ckuzma/dipole-antenna/media/02-element-holder-beta-tinkercad.png

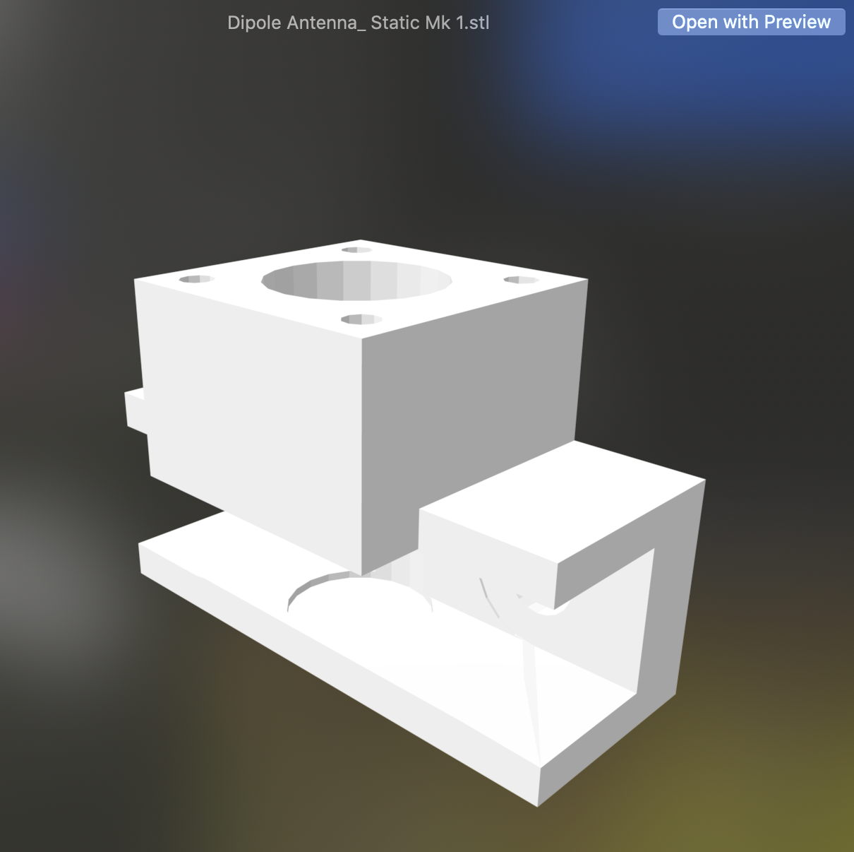
media/02-element-holder-beta-tinkercad.png
