ckuzma/dipole-antenna/media/03-so239-plug-freecad.png

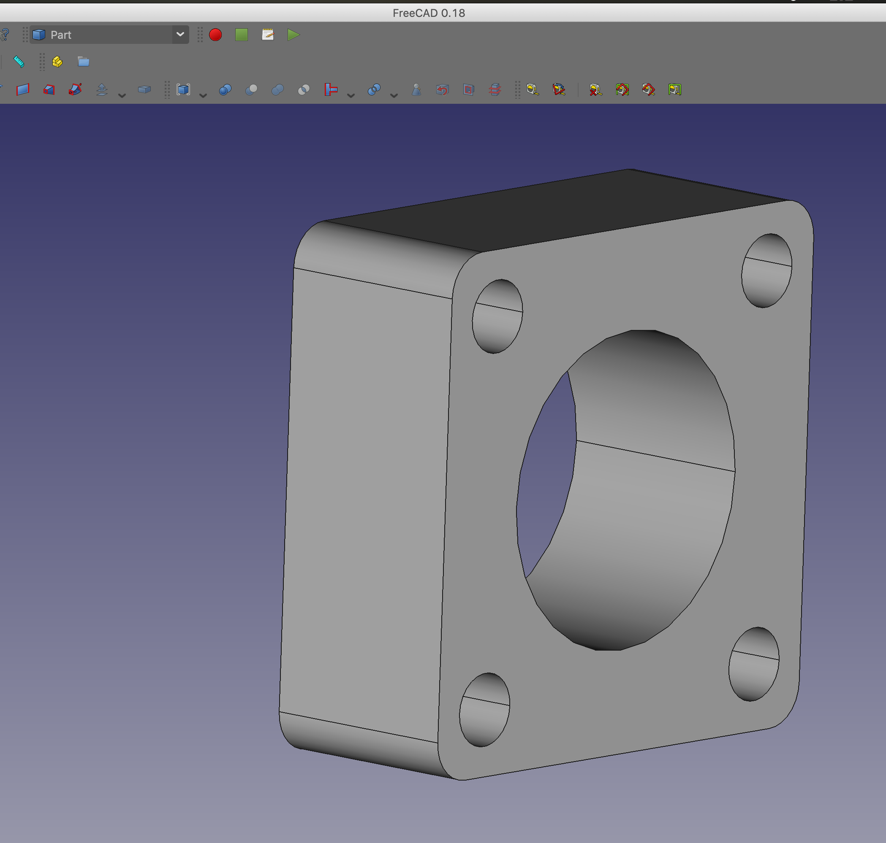
media/03-so239-plug-freecad.png
