ckuzma/dipole-antenna/media/04-element-holder-mk1-freecad.png

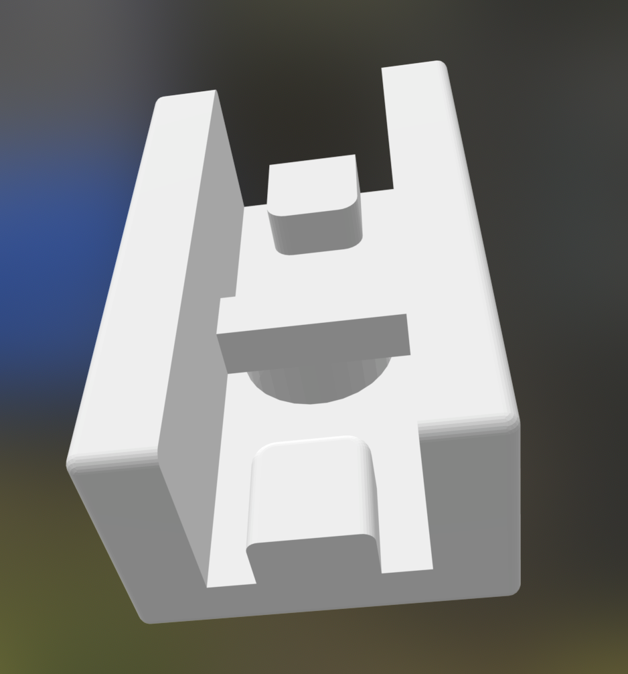
media/04-element-holder-mk1-freecad.png
