ckuzma/dipole-antenna/media/05-element-holder-mk1-freecad.png

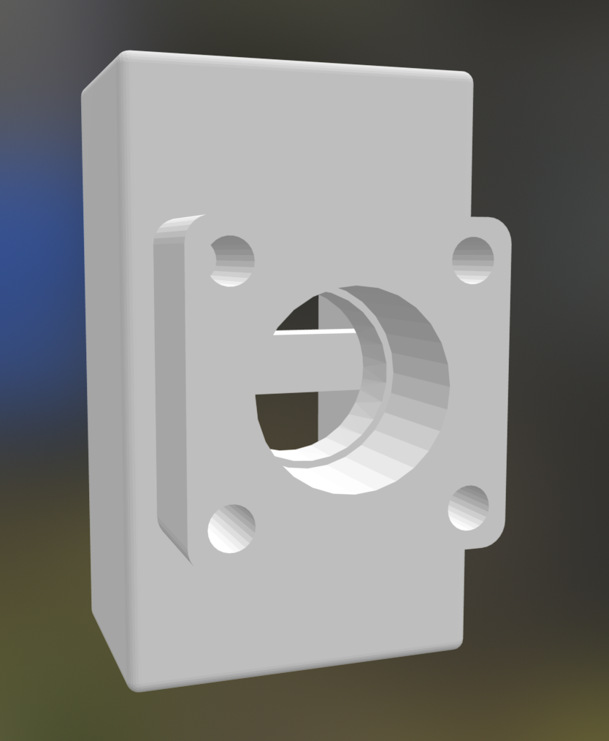
media/05-element-holder-mk1-freecad.png
