ckuzma/dipole-antenna/media/File_000.jpeg

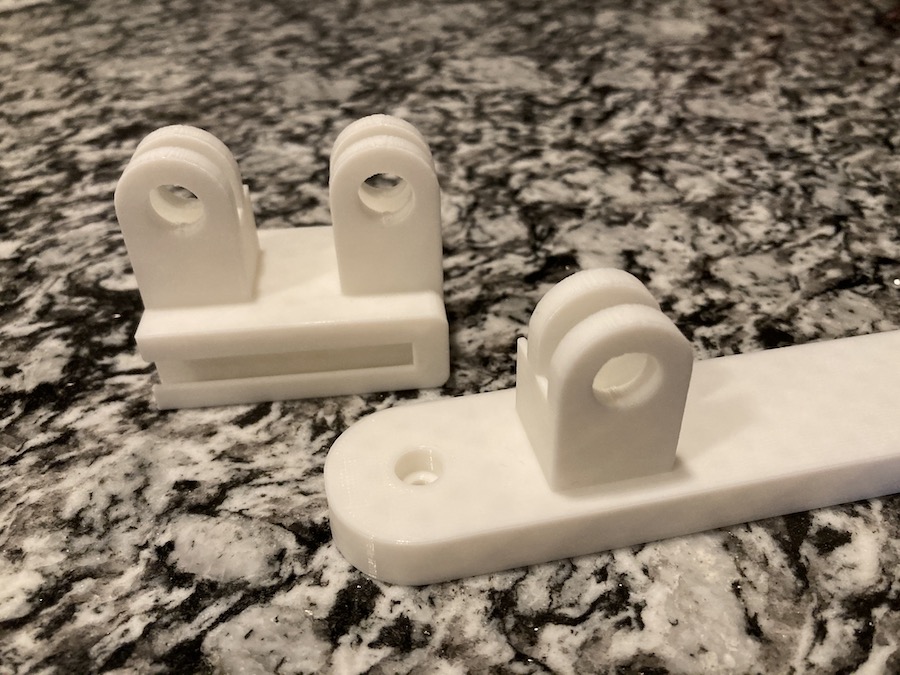
media/File_000.jpeg
