ckuzma/dipole-antenna/media/File_001.jpeg

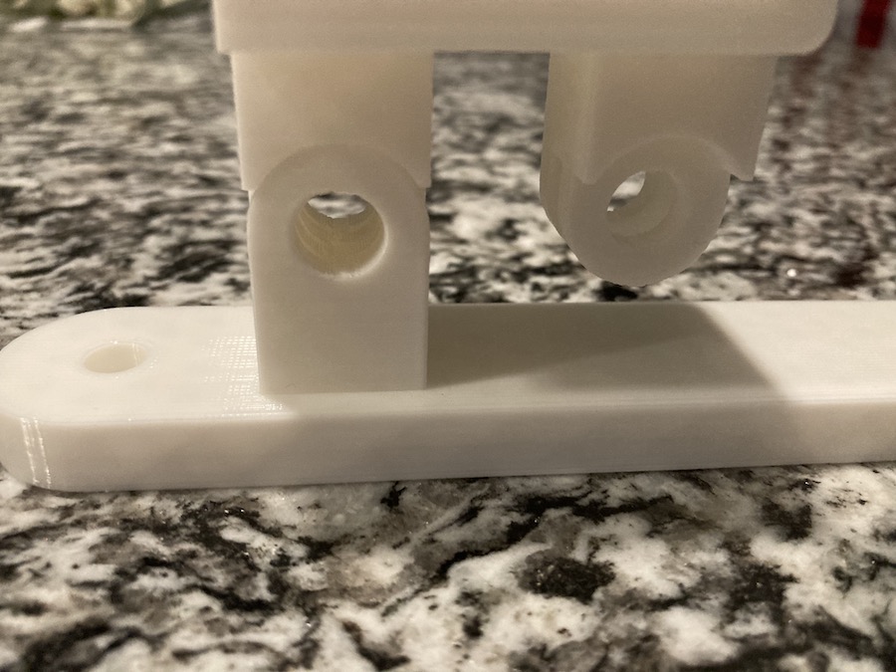
media/File_001.jpeg
