ckuzma/dipole-antenna/media/File_002.jpeg

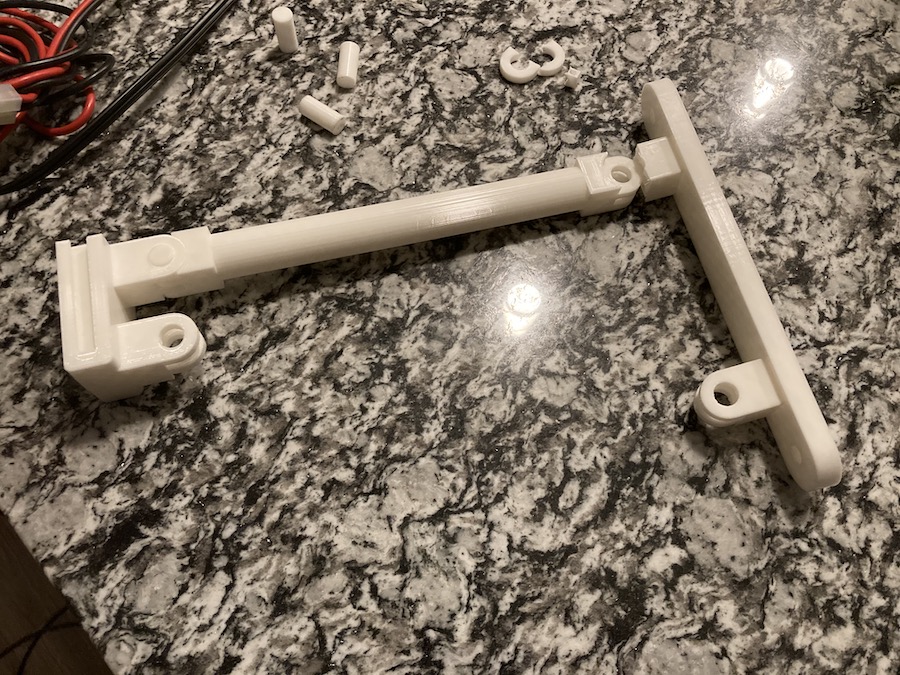
media/File_002.jpeg
