ckuzma/dipole-antenna/media/File_003.jpeg

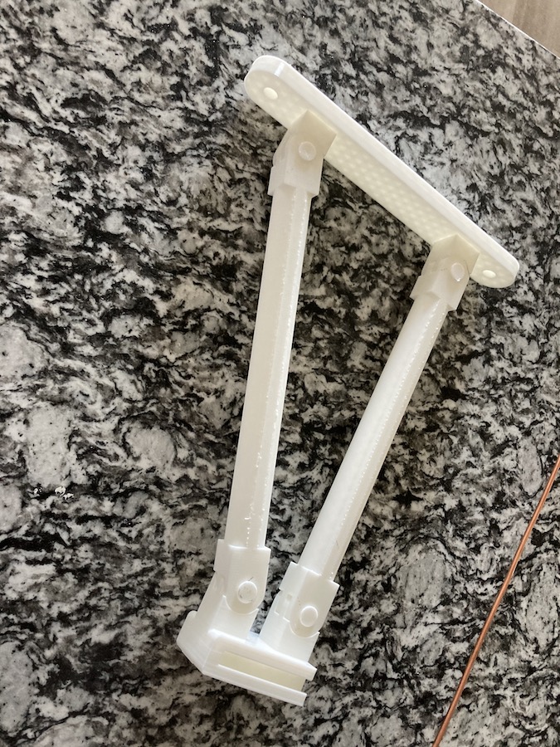
media/File_003.jpeg
