ckuzma/dipole-antenna/media/File_004.jpeg

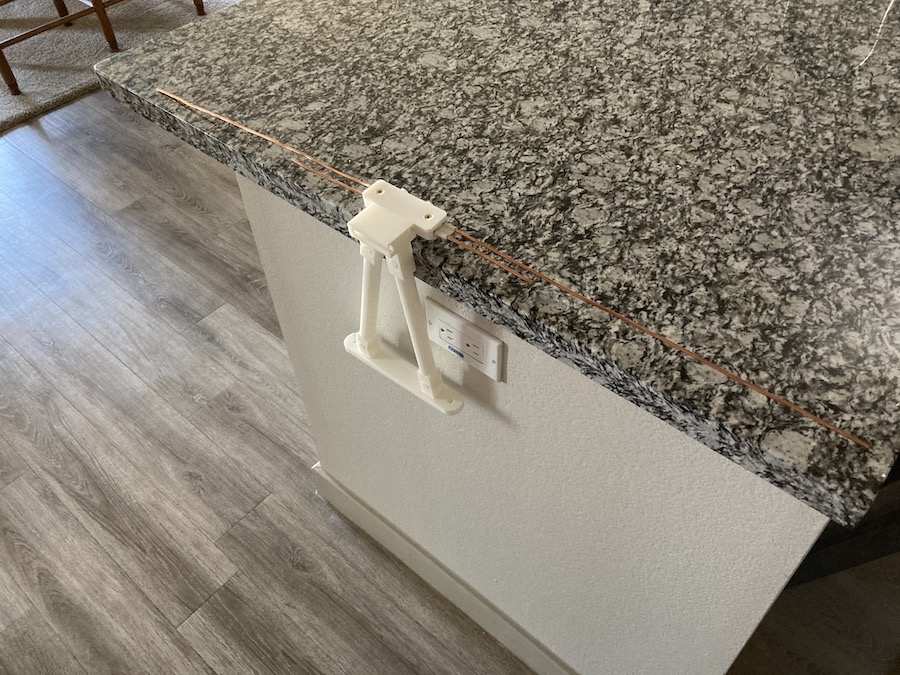
media/File_004.jpeg
