ckuzma/dipole-antenna/media/File_005.jpeg

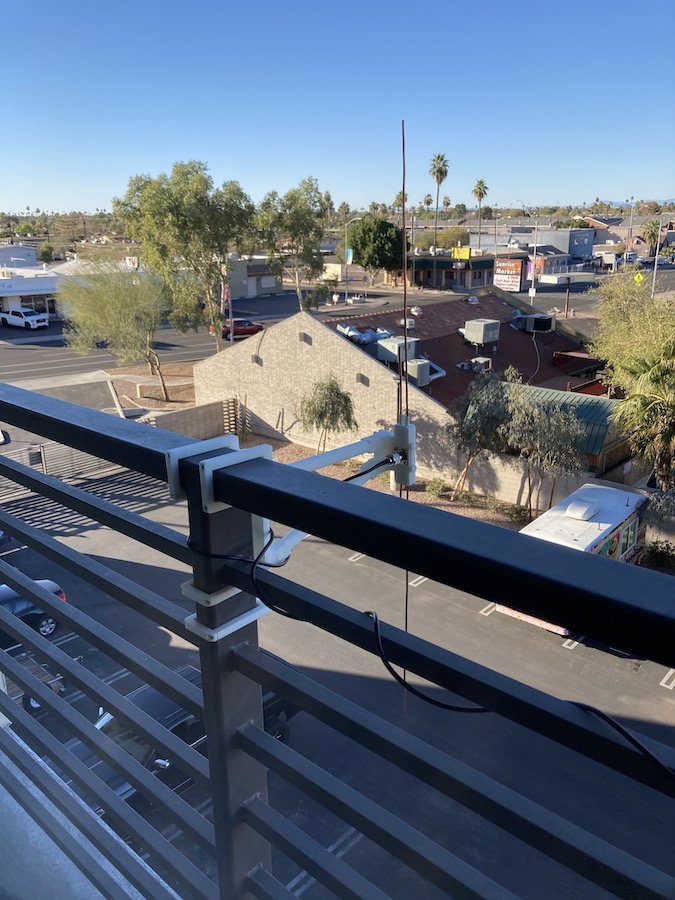
media/File_005.jpeg
