ckuzma/dipole-antenna/media/File_007.jpeg

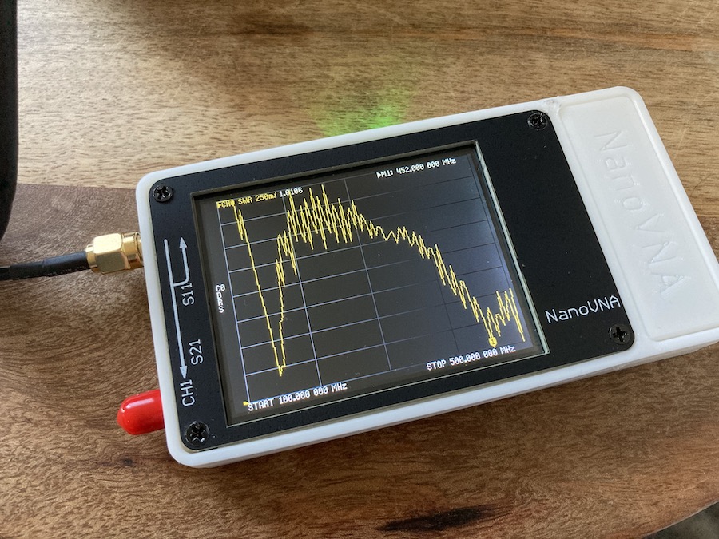
media/File_007.jpeg
