ckuzma/dipole-antenna/media/File_008.jpeg

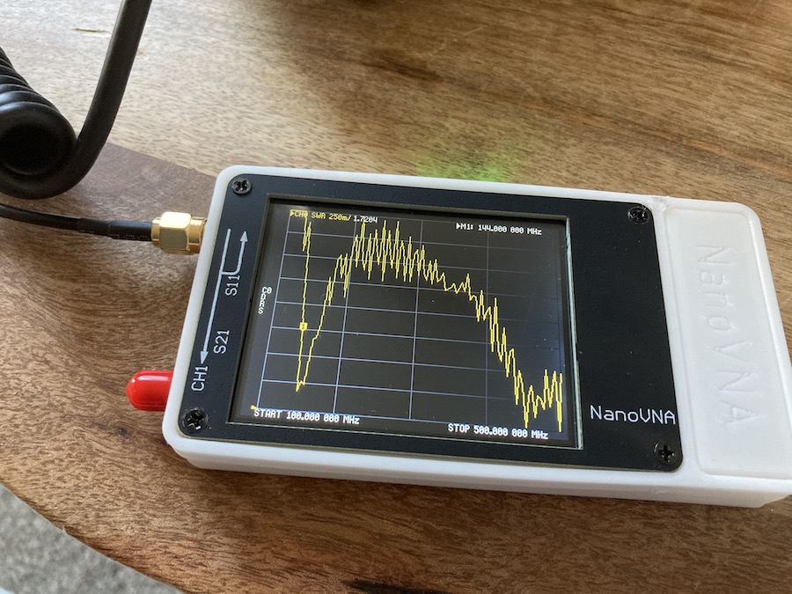
media/File_008.jpeg
