ckuzma/dipole-antenna/media/File_009.jpeg

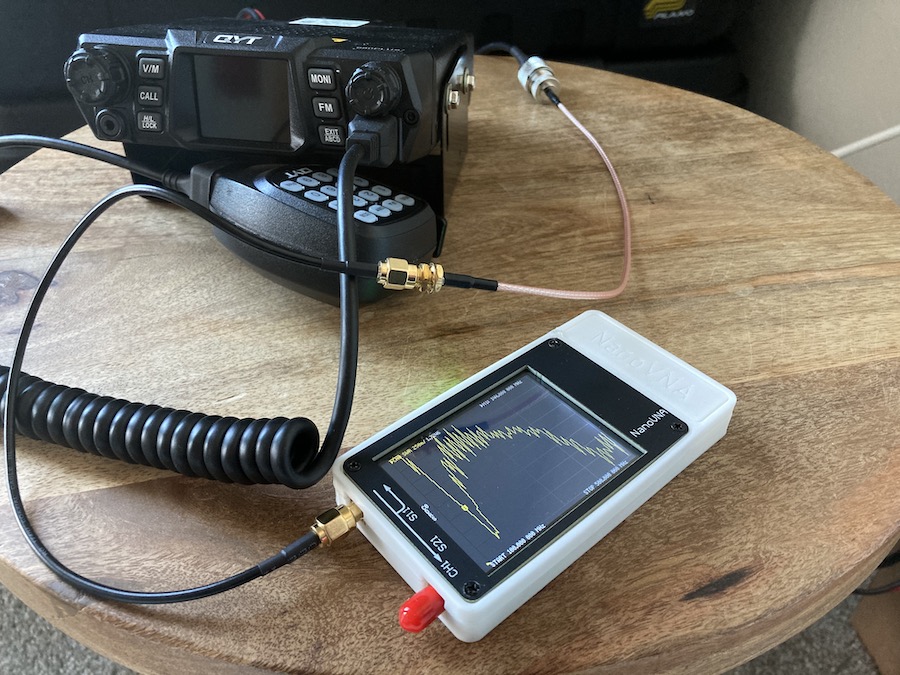
media/File_009.jpeg
