ckuzma/dipole-antenna/new-implementation/strut-bottom.stl

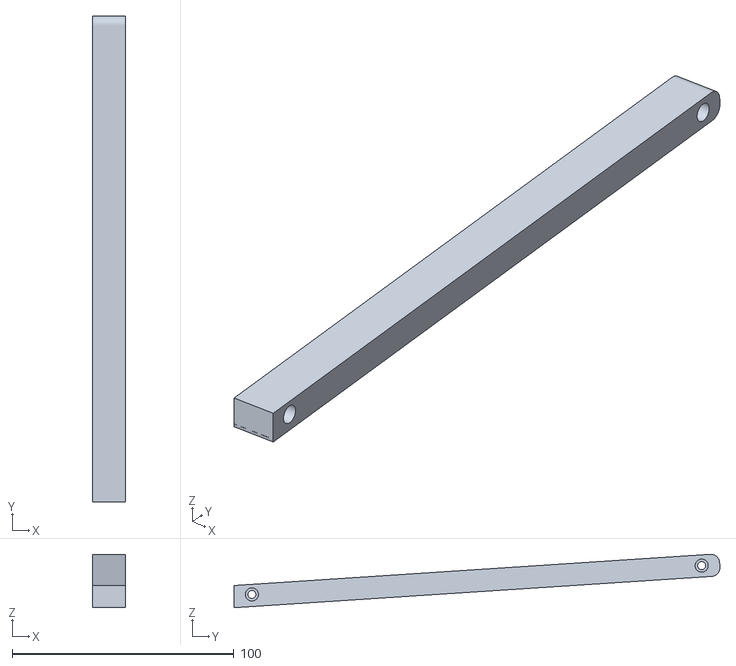
[picture p40: CAD file, 2022-08-23]
new-implementation/strut-bottom.stl
15.0 x 219.3 x 24.1
