ckuzma/dipole-antenna/freecad_models/antenna-sheath.FCStd

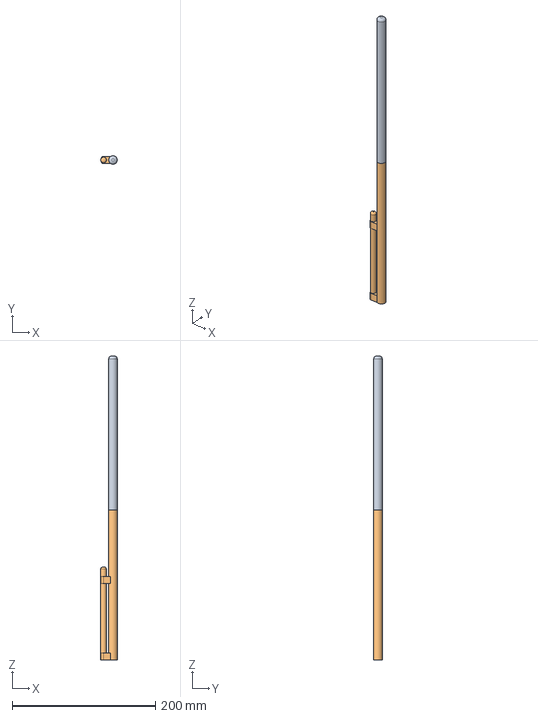
[picture p41: CAD file, 2021-02-18]
freecad_models/antenna-sheath.FCStd
23.2 x 12.0 x 425.0 mm
VHF-higher
Joint Lower VHF UHF
