ckuzma/dipole-antenna/freecad_models/components/so239.FCStd

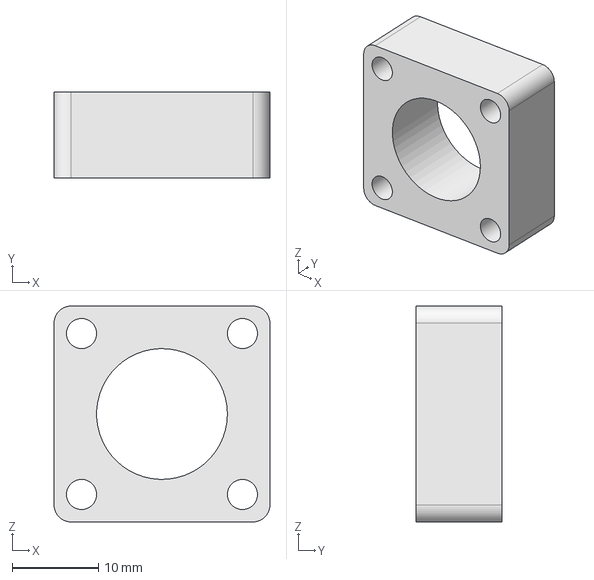
[picture p42: CAD file, 2021-02-10]
freecad_models/components/so239.FCStd
25.1 x 10.0 x 25.1 mm
