ckuzma/dipole-antenna/freecad_models/wall_holder/pivots-a-b.FCStd

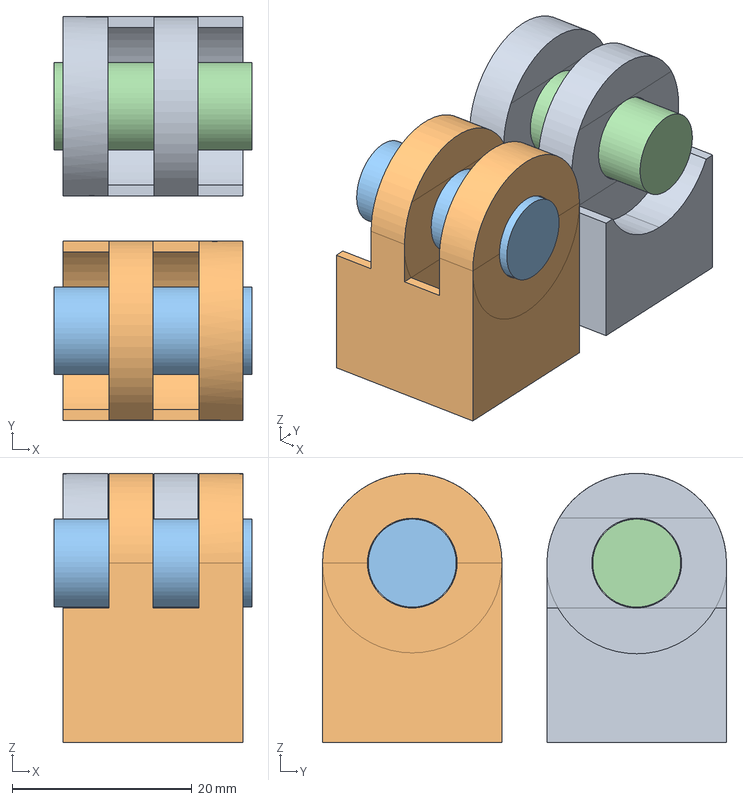
[picture p43: CAD file, 2021-02-16]
freecad_models/wall_holder/pivots-a-b.FCStd
22.0 x 45.0 x 30.0 mm
Pivot-A
Pivot-B
Pivot-B-Pin
Pivot-A-Pin
