ckuzma/dipole-antenna/new-implementation/strut-top.stl

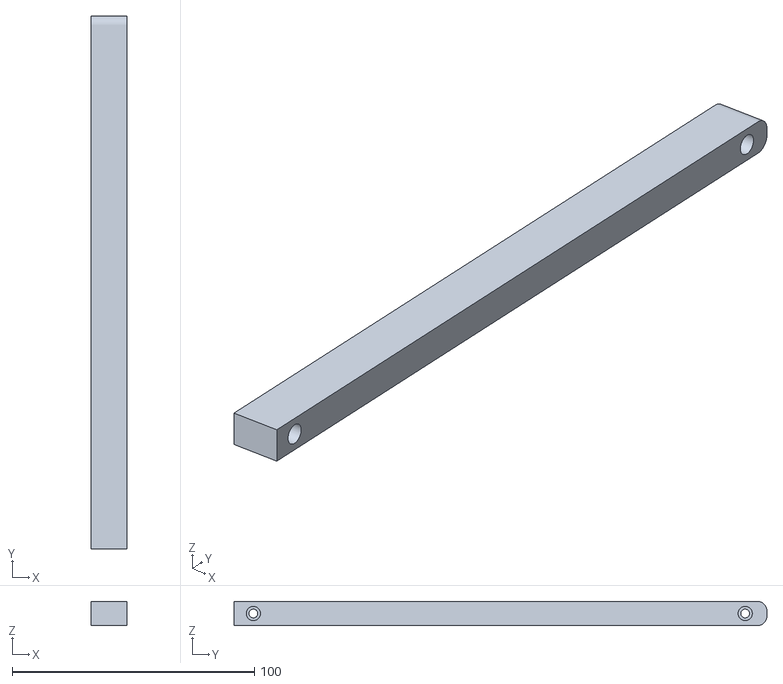
[picture p44: CAD file, 2022-08-23]
new-implementation/strut-top.stl
15.0 x 220.0 x 10.0
