ckuzma/dipole-antenna/freecad_models/holder-top.FCStd

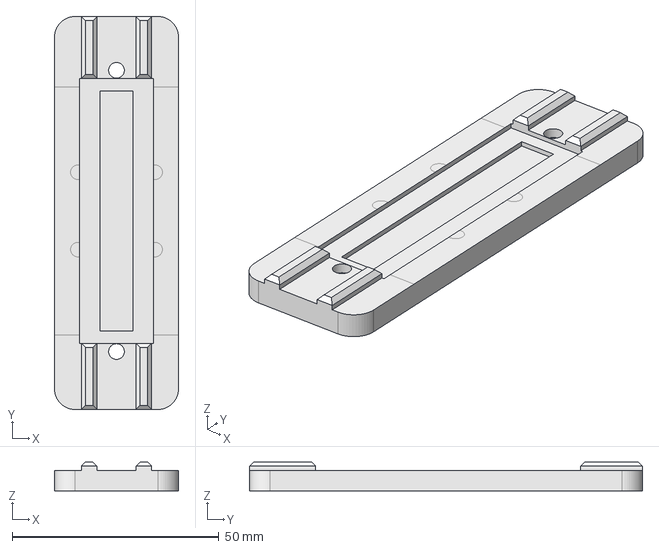
[picture p45: CAD file, 2021-02-11]
freecad_models/holder-top.FCStd
30.0 x 95.0 x 7.00 mm
