ckuzma/dipole-antenna/new-implementation/top-clamp-end.stl

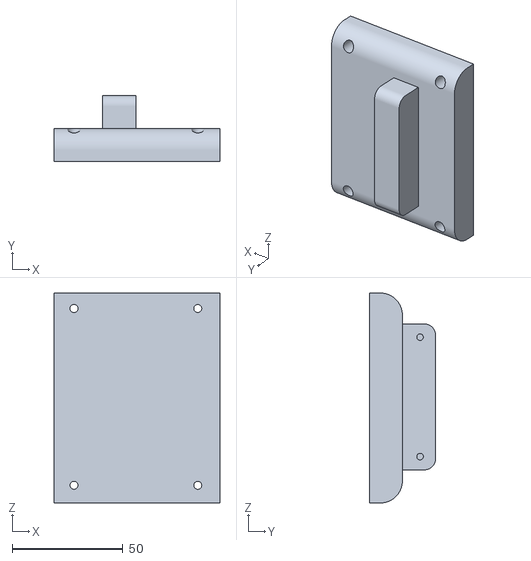
[picture p46: CAD file, 2022-08-23]
new-implementation/top-clamp-end.stl
75.0 x 29.9 x 95.0
