ckuzma/dipole-antenna/freecad_models/holder-bottom.FCStd

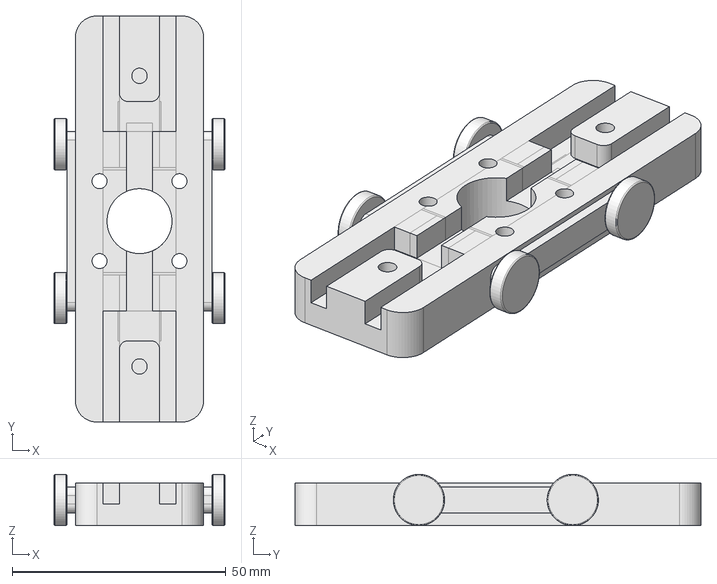
[picture p47: CAD file, 2021-02-10]
freecad_models/holder-bottom.FCStd
40.0 x 95.0 x 12.0 mm
