ckuzma/dipole-antenna/new-implementation/slotted-hub.FCStd

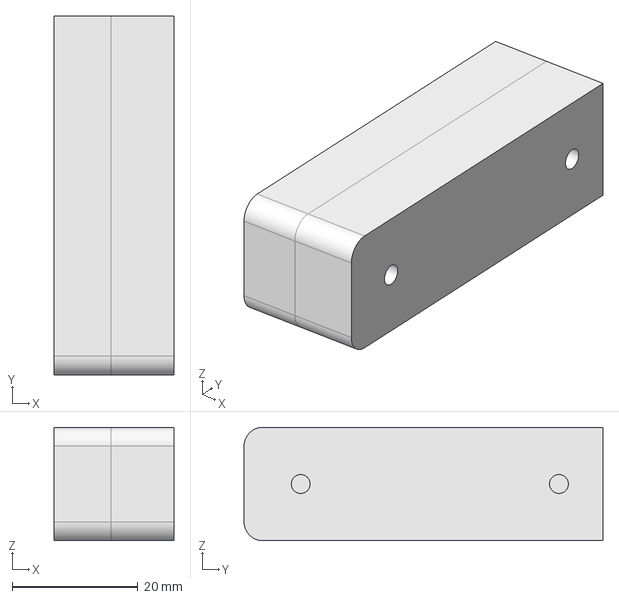
[picture p48: CAD file, 2022-08-23]
new-implementation/slotted-hub.FCStd
19.0 x 57.0 x 18.0 mm
