ckuzma/dipole-antenna/new-implementation/railing-mockup.FCStd

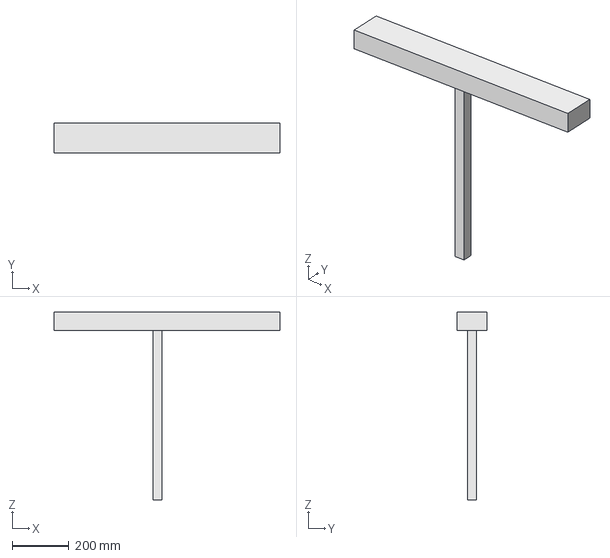
[picture p49: CAD file, 2022-08-23]
new-implementation/railing-mockup.FCStd
800.0 x 105.1 x 664.0 mm
