ckuzma/dipole-antenna/media/build-documentation/File_001.jpeg

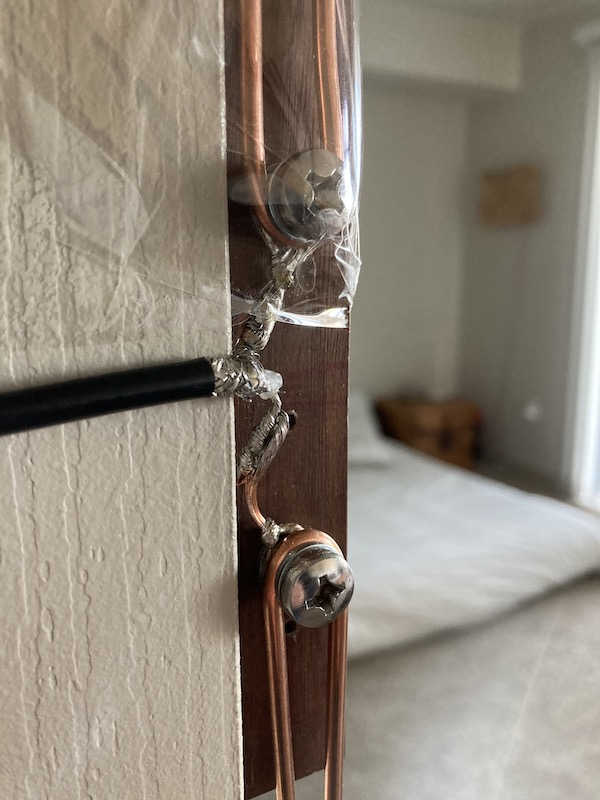
media/build-documentation/File_001.jpeg
