ckuzma/dipole-antenna/media/build-documentation/File_005.jpeg

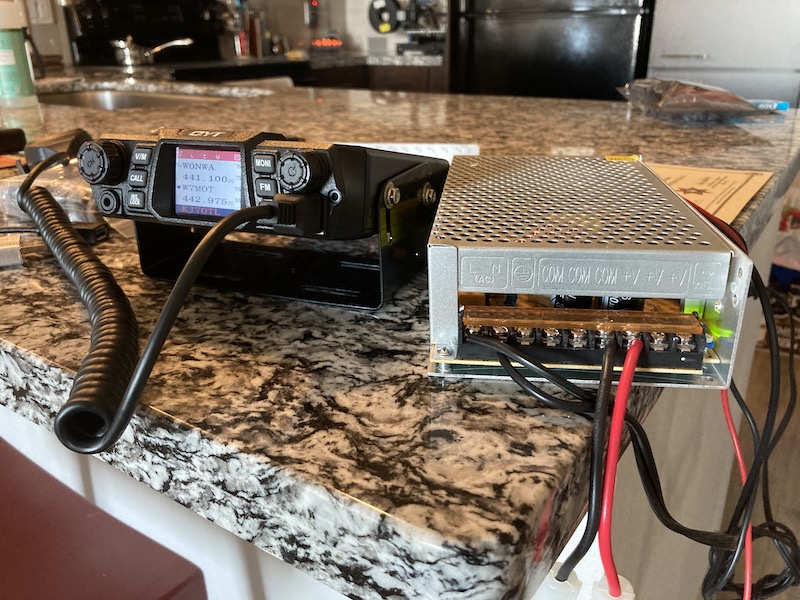
media/build-documentation/File_005.jpeg
