ckuzma/dipole-antenna/media/build-documentation/File_013.jpeg

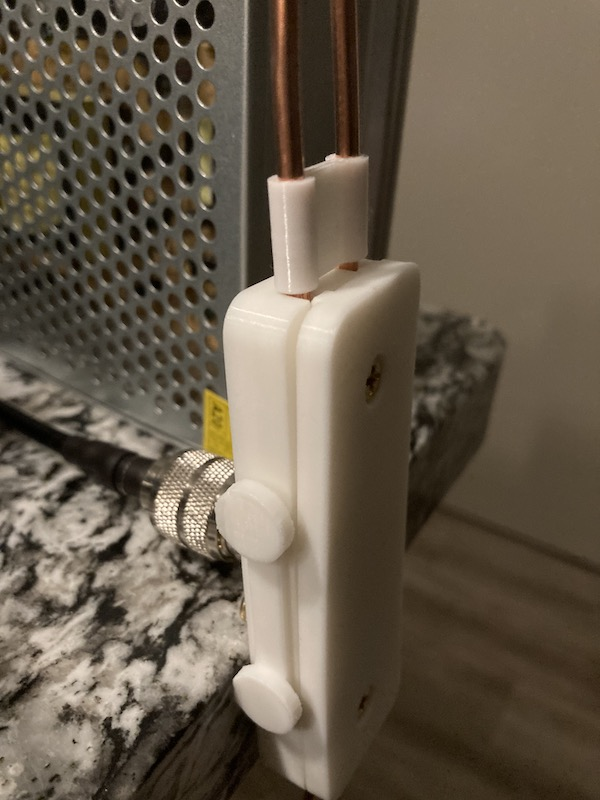
media/build-documentation/File_013.jpeg
